inopya/BIG-Digit/firmware/big_digit_basic/pinout.h

/*
  ----------------------------------------
           << PINOUT  MAP >>
  ----------------------------------------
*/


/*mmmmmmmmmmmmmmmmmmmmmmmmmmmmmmmmmmmmmmmmmmmmmmmmmmmmmmmmmmmmmmmmmmmmmmmmmmmmmmmmmmmmmmmmmmmmmmmmmmm
//        DEFINICION DE PINES
//mmmmmmmmmmmmmmmmmmmmmmmmmmmmmmmmmmmmmmmmmmmmmmmmmmmmmmmmmmmmmmmmmmmmmmmmmmmmmmmmmmmmmmmmmmmmmmmmmmm*/

#define PIN_LED_OnBoard             13    // Led on Board Wemos
#define PIN_sensorNTC               A0
#define PIN_TIRA_LED				         9
